brickbots/HandiPi/images/beauty/IMG_8138.jpeg

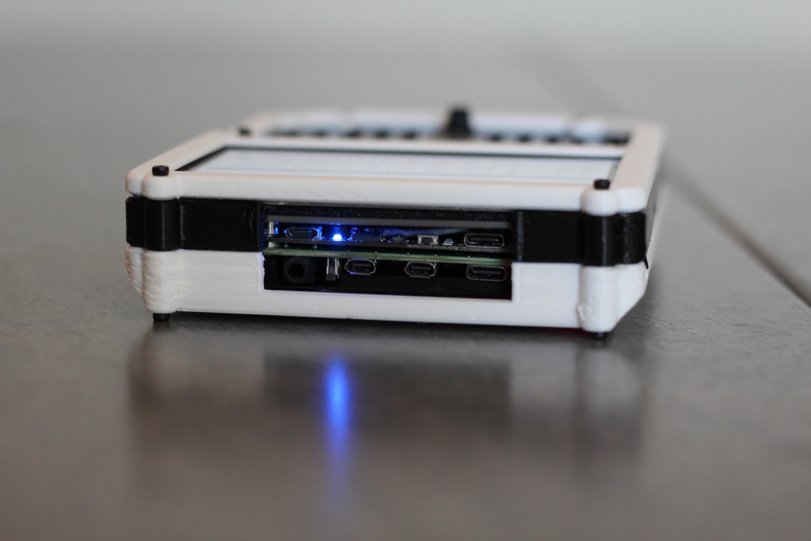
images/beauty/IMG_8138.jpeg
