brickbots/HandiPi/images/build/IMG_8169.jpeg

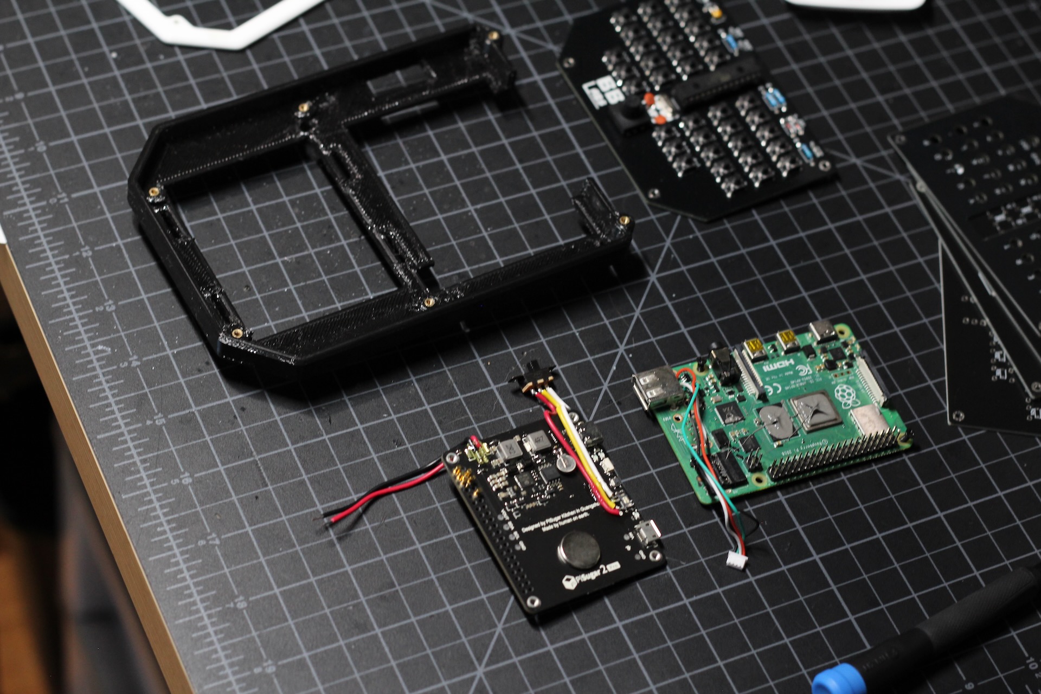
images/build/IMG_8169.jpeg
